Barosandu/TSC-Openbook/Images/Screenshot 2025-04-14 at 20.05.11.png

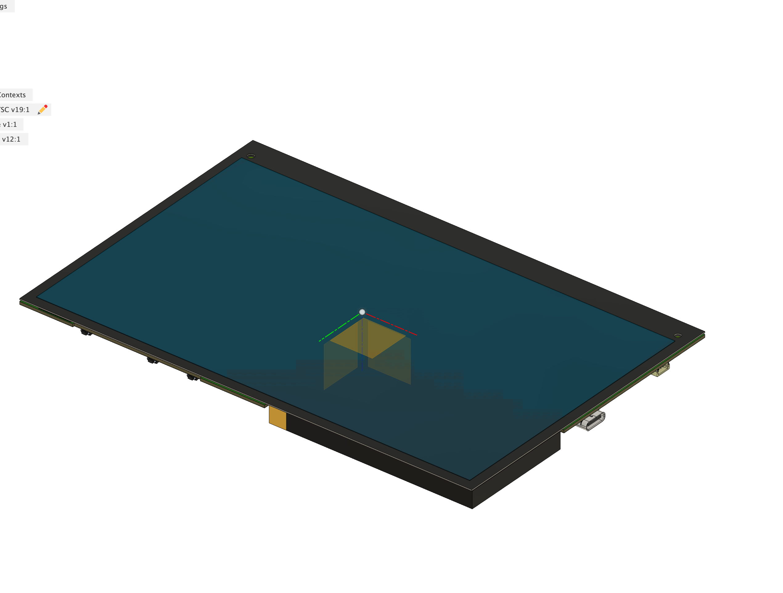
Images/Screenshot 2025-04-14 at 20.05.11.png
